zxcand/PET/models/v5/powerbank.SLDPRT

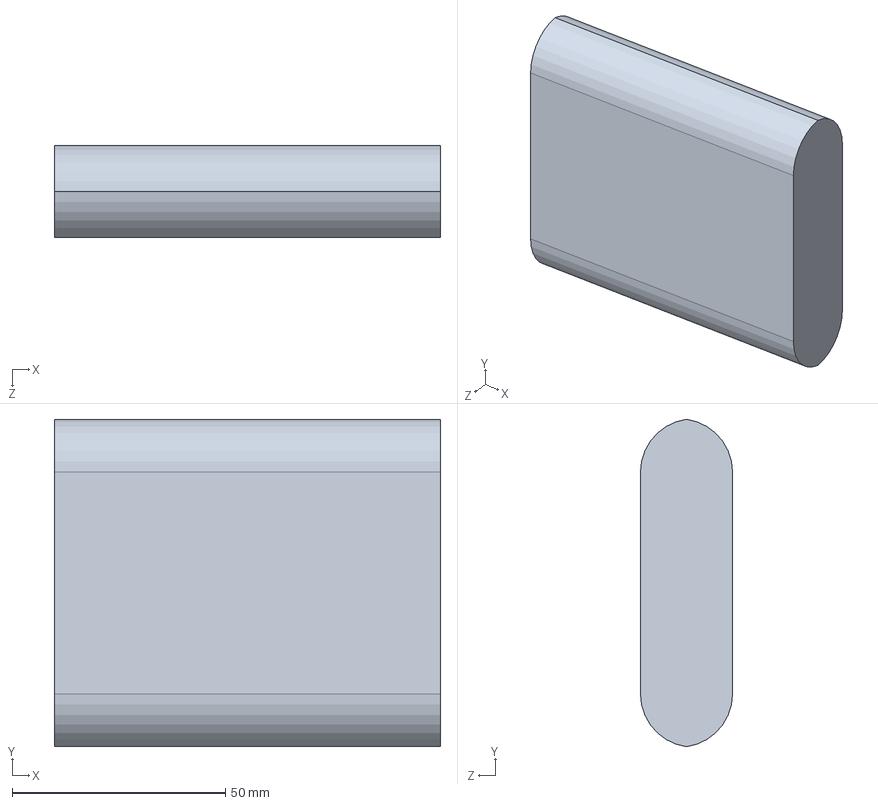
[picture p15: CAD file, 2015-07-02]
models/v5/powerbank.SLDPRT
90.5 x 76.8 x 21.6 mm
