zxcand/PET/models/v5/base_COVER_top.SLDPRT

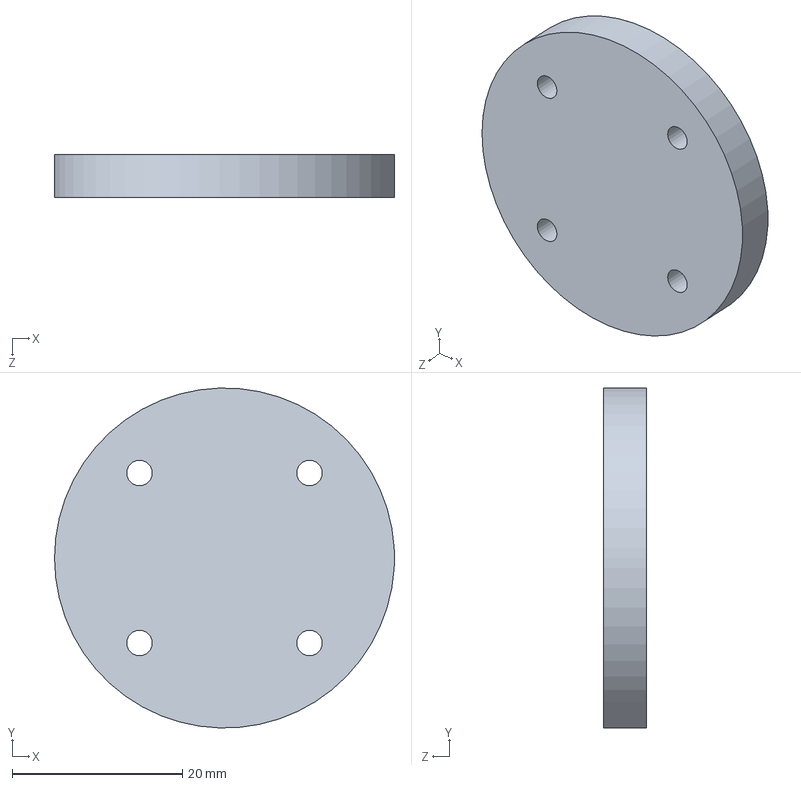
[picture p16: CAD file, 2015-07-02]
models/v5/base_COVER_top.SLDPRT
40.0 x 40.0 x 5.00 mm
