zxcand/PET/models/v5/base_laser.SLDPRT

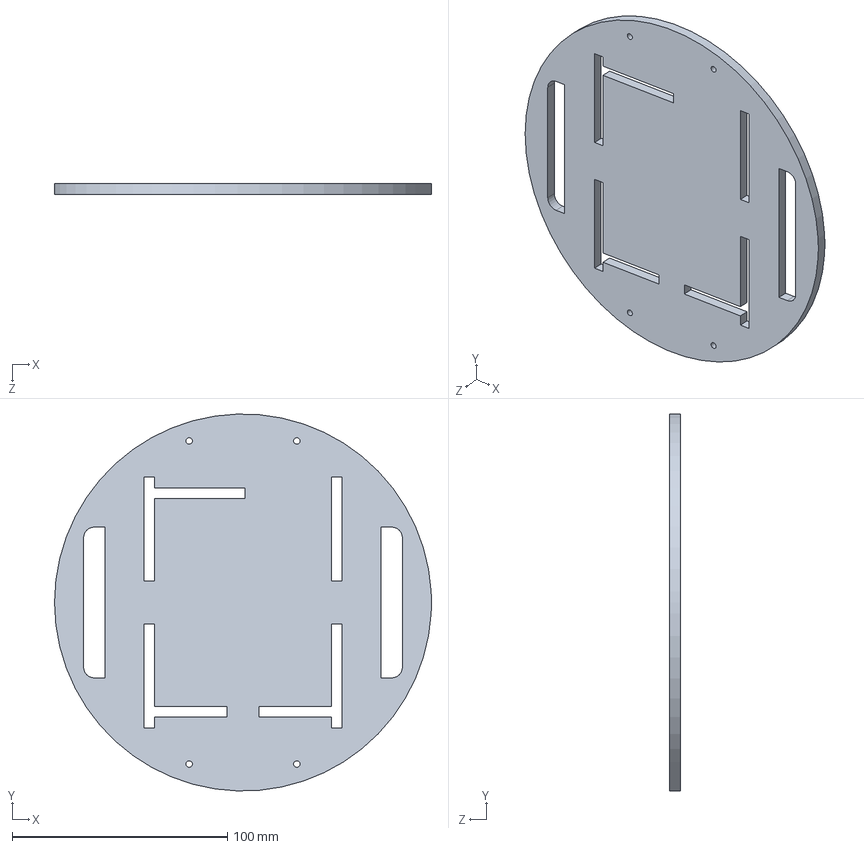
[picture p17: CAD file, 2015-07-02]
models/v5/base_laser.SLDPRT
175.0 x 174.9 x 5.00 mm
