zxcand/PET/models/v5/base.SLDPRT

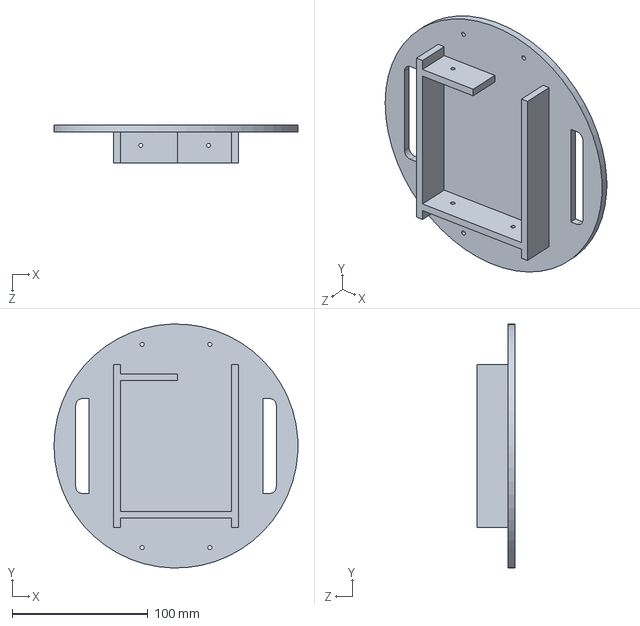
[picture p18: CAD file, 2015-07-02]
models/v5/base.SLDPRT
180.0 x 179.9 x 28.0 mm
