zxcand/PET/models/v5/Motor.SLDPRT

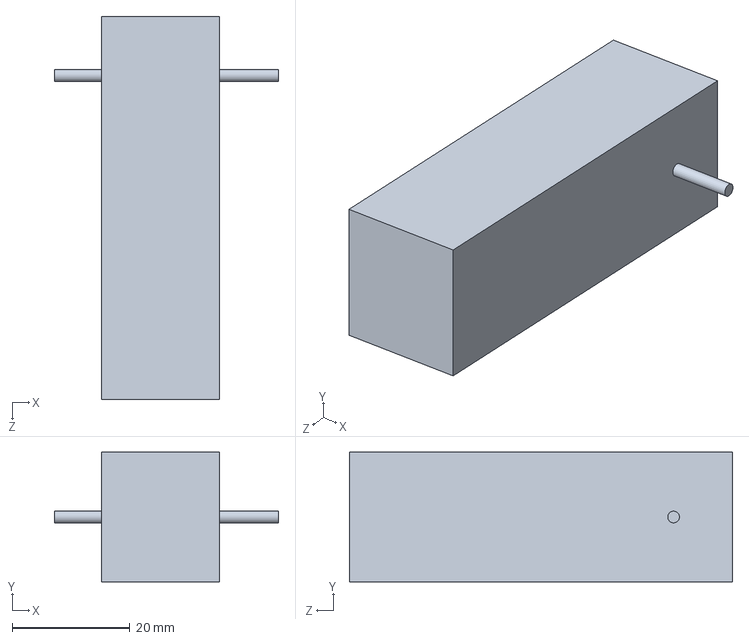
[picture p19: CAD file, 2015-07-02]
models/v5/Motor.SLDPRT
38.0 x 22.0 x 65.0 mm
