zxcand/PET/models/v5/asus_powerbank.SLDPRT

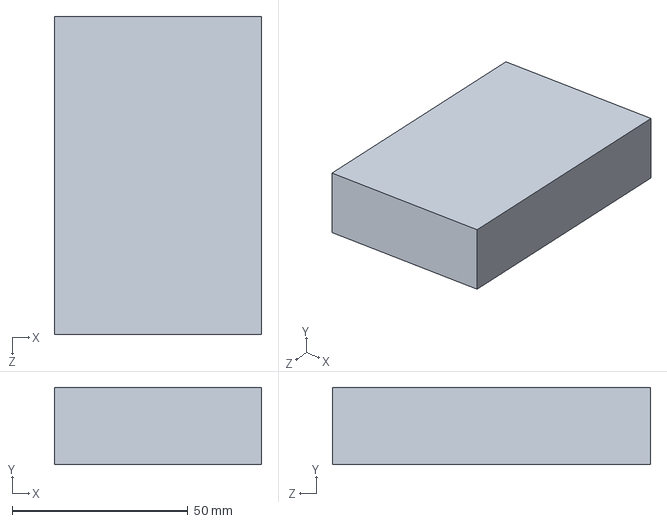
[picture p20: CAD file, 2015-07-02]
models/v5/asus_powerbank.SLDPRT
59.0 x 22.0 x 90.5 mm
