zxcand/PET/models/v5/wheel.SLDPRT

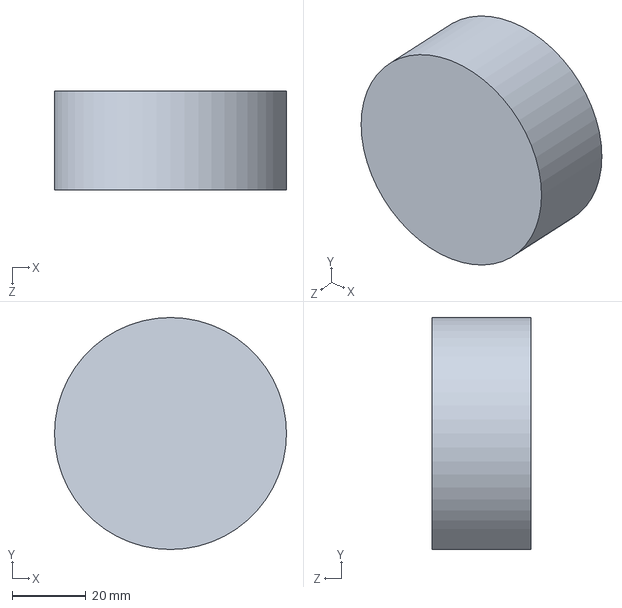
[picture p21: CAD file, 2015-07-02]
models/v5/wheel.SLDPRT
63.0 x 63.0 x 27.0 mm
